DaMiBear/ESP32_HomeKit_AirConditioner/docs/images/11.PNG

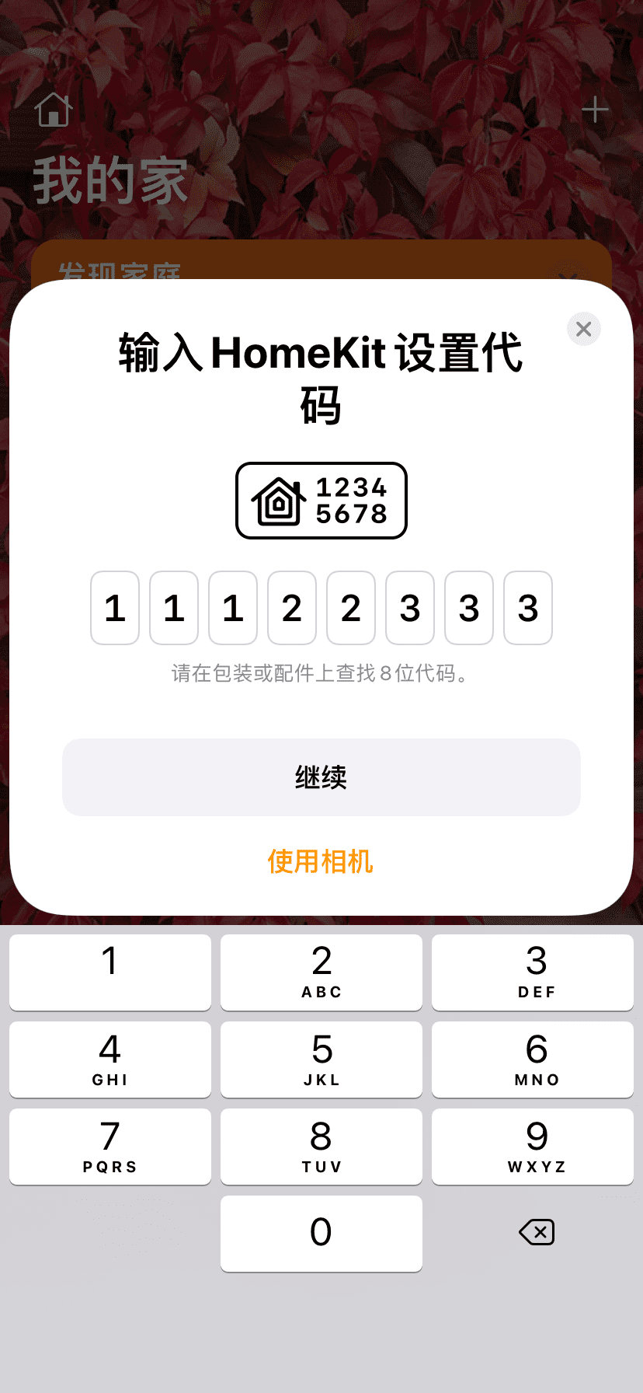
docs/images/11.PNG
